Tintun1/ProyectoRFID/AppWeb/uploads/20230421_070830.jpg

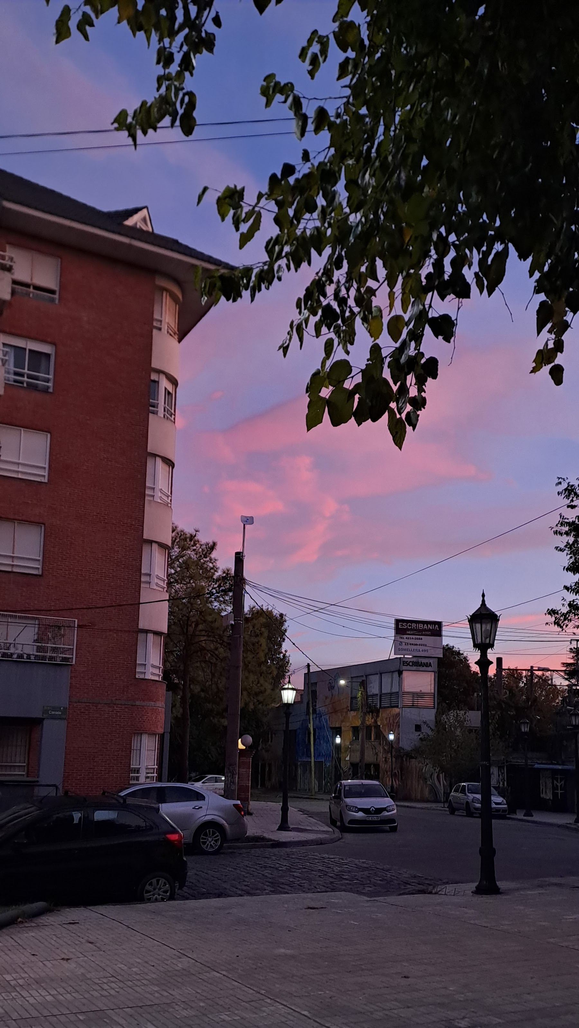
AppWeb/uploads/20230421_070830.jpg
