Tintun1/ProyectoRFID/AppWeb/uploads/IMG-20230510-WA0010.jpg

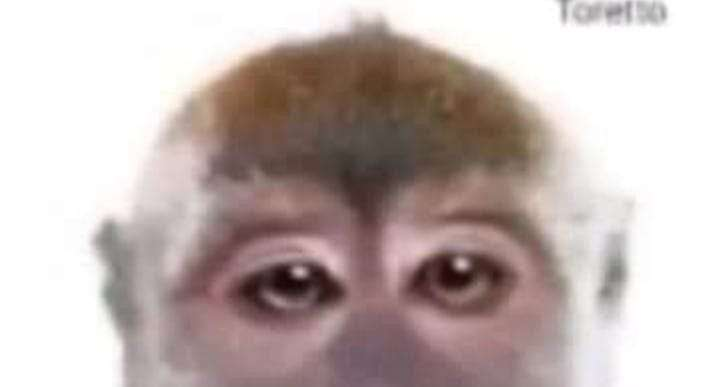
AppWeb/uploads/IMG-20230510-WA0010.jpg
