Tintun1/ProyectoRFID/AppWeb/uploads/IMG-20230916-WA0011.jpg

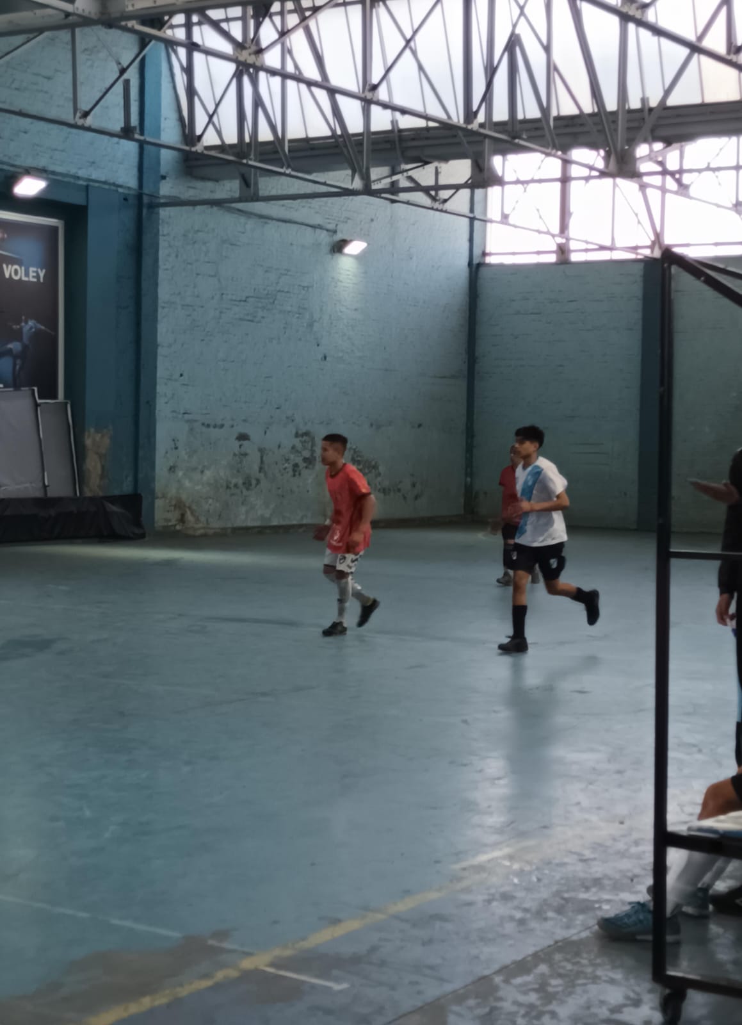
AppWeb/uploads/IMG-20230916-WA0011.jpg
