Tintun1/ProyectoRFID/AppWeb/uploads/IMG-20240312-WA0022.jpg

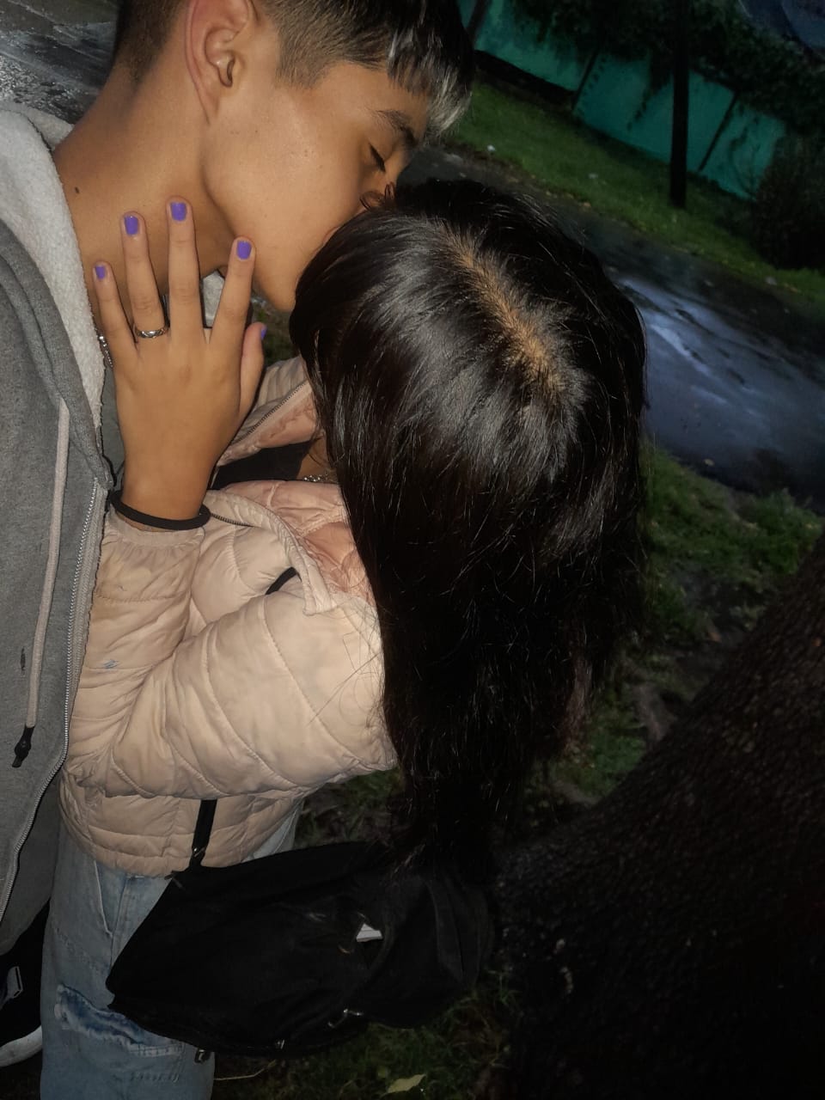
AppWeb/uploads/IMG-20240312-WA0022.jpg
