Tintun1/ProyectoRFID/AppWeb/uploads/IMG_20240212_182841_012.jpg

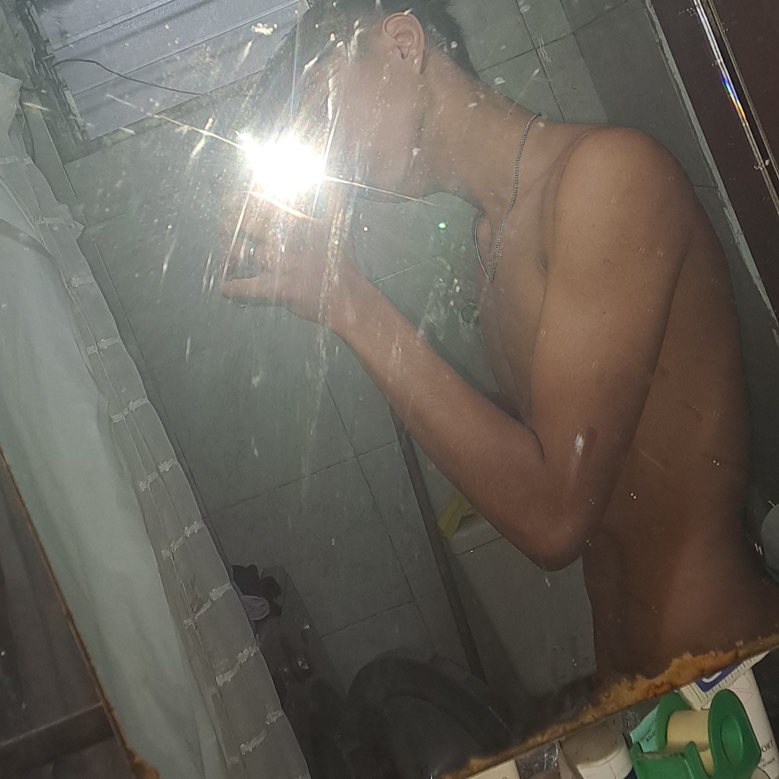
AppWeb/uploads/IMG_20240212_182841_012.jpg
