Tintun1/ProyectoRFID/AppWeb/uploads/OIG4.jpg

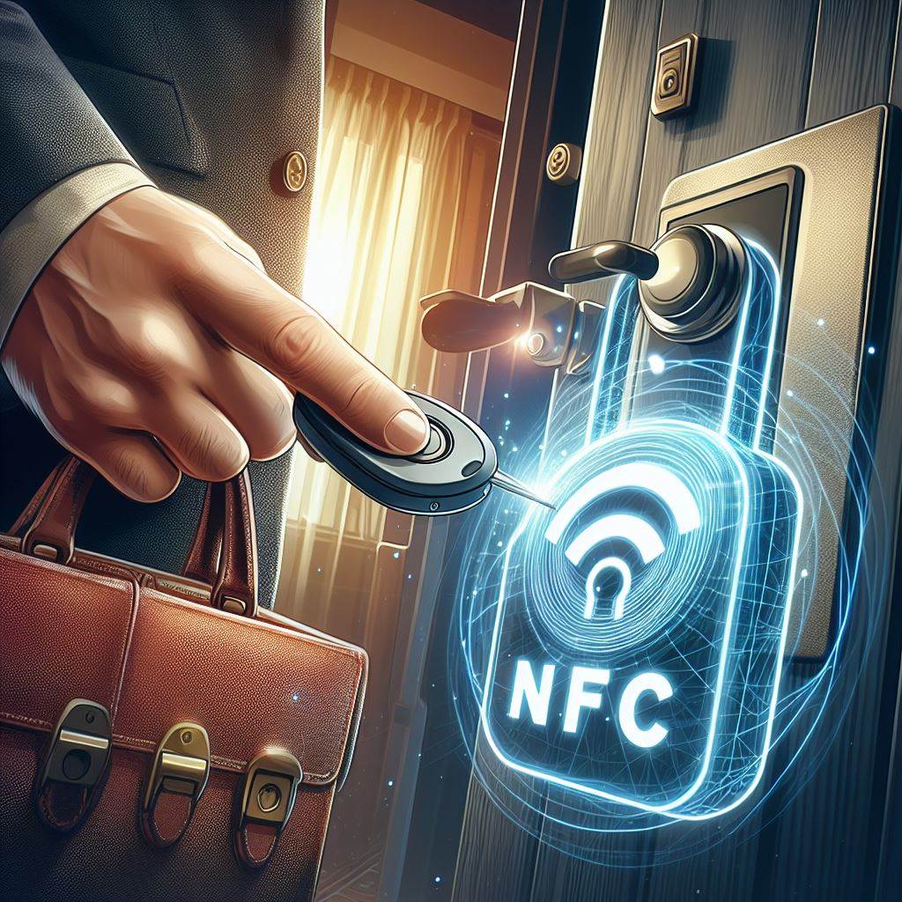
AppWeb/uploads/OIG4.jpg
