Tintun1/ProyectoRFID/AppWeb/uploads/profile_pic_default.jpeg

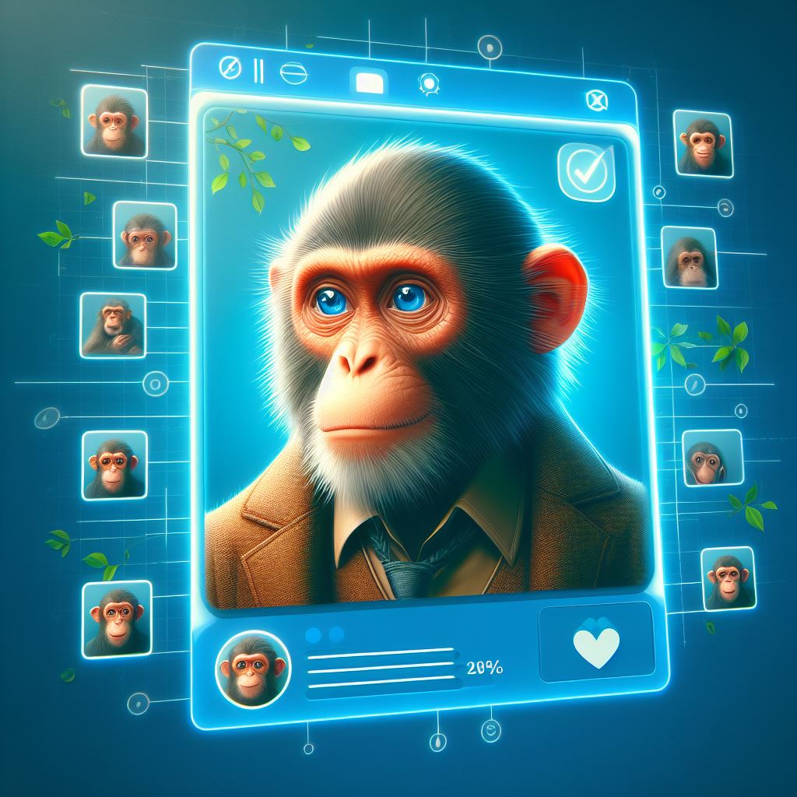
AppWeb/uploads/profile_pic_default.jpeg
