Tintun1/ProyectoRFID/AppWeb/uploads/Screenshot_20240402_022424_WhatsApp.jpg

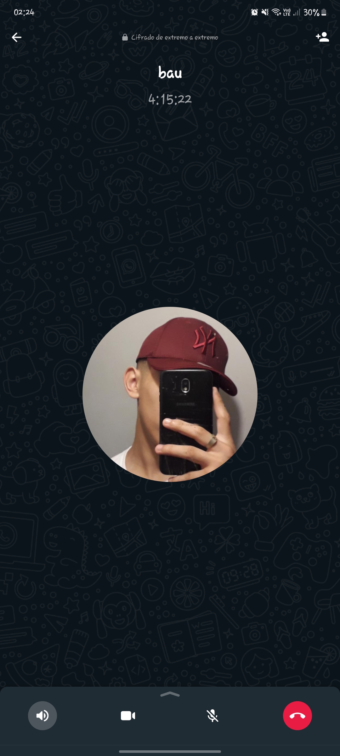
AppWeb/uploads/Screenshot_20240402_022424_WhatsApp.jpg
