Tintun1/ProyectoRFID/AppWeb/uploads/skype-monkey.gif

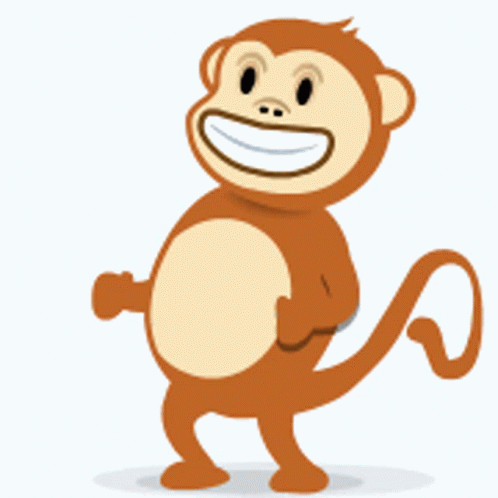
AppWeb/uploads/skype-monkey.gif
