Tintun1/ProyectoRFID/Documentos Kicad/Placa NFC/Documentos/pcbshield_2_2.png

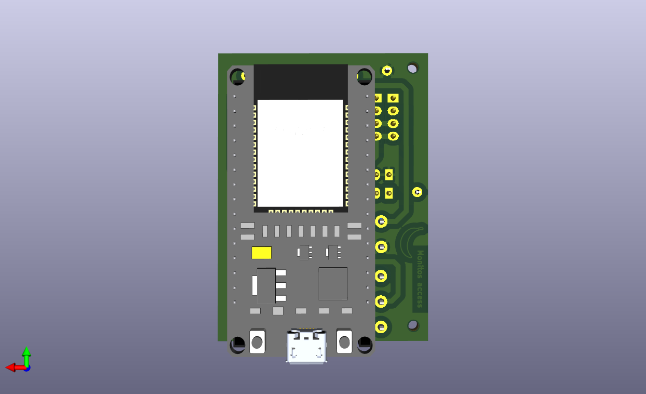
Documentos Kicad/Placa NFC/Documentos/pcbshield_2_2.png
